Happily-Coding/SweepyWay/research case 2025-08-03/Pensando como encarar handrest.png

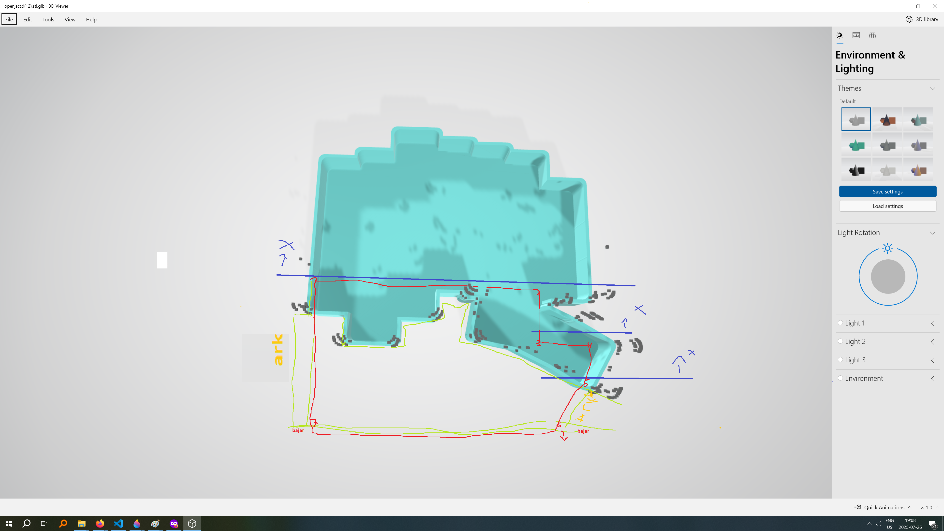
research case 2025-08-03/Pensando como encarar handrest.png
