Happily-Coding/SweepyWay/filtered-output/pcbs/outlines/l_hand_rest_polygon.dxf

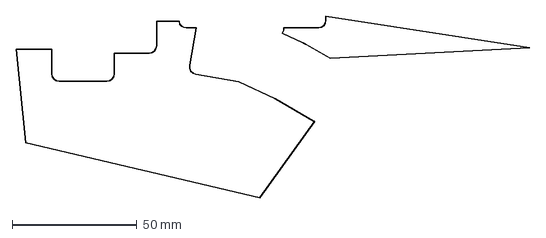
[picture p26: CAD file, 2026-02-16]
filtered-output/pcbs/outlines/l_hand_rest_polygon.dxf
206.0 x 72.7 mm
