Happily-Coding/SweepyWay/research case 2025-08-03/pymodeling_tests/lofted_polyhedron_clean.stl

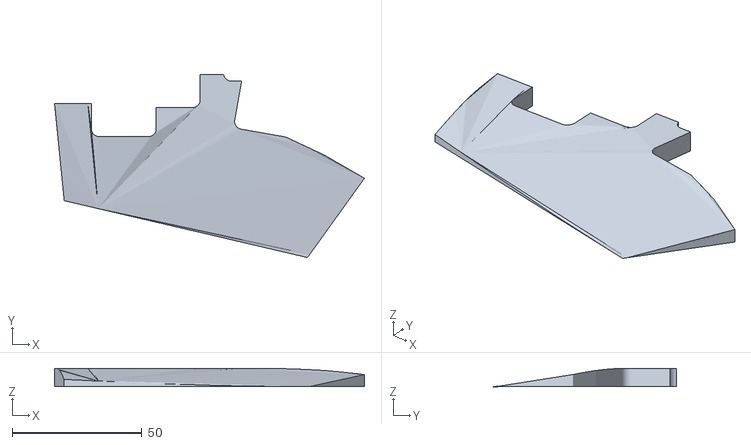
[picture p27: CAD file, 2025-08-17]
research case 2025-08-03/pymodeling_tests/lofted_polyhedron_clean.stl
119.6 x 70.7 x 7.00
