Happily-Coding/SweepyWay/filtered-output/pcbs/outlines/r_controller_area_border.dxf

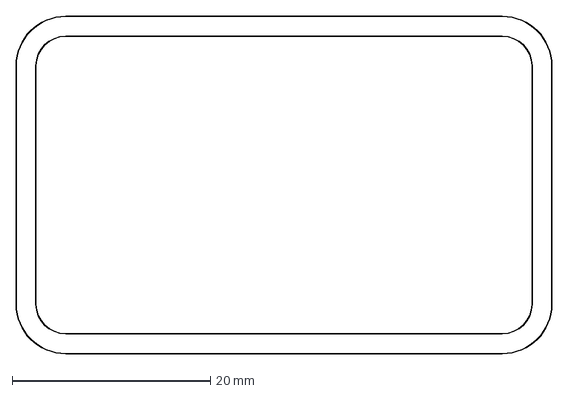
[picture p28: CAD file, 2026-02-16]
filtered-output/pcbs/outlines/r_controller_area_border.dxf
54.0 x 34.0 mm
