Happily-Coding/SweepyWay/research case 2025-08-03/pymodeling_tests/solid_lofted_mesh.stl

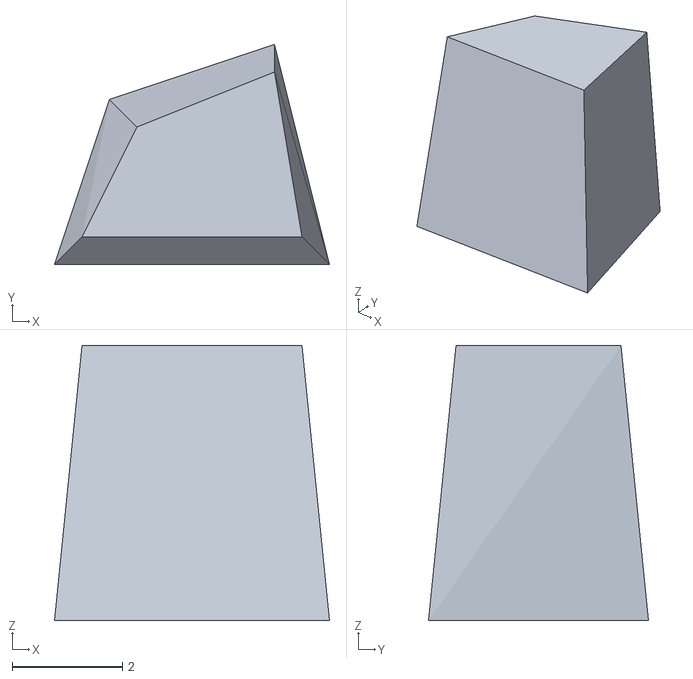
[picture p29: CAD file, 2025-08-17]
research case 2025-08-03/pymodeling_tests/solid_lofted_mesh.stl
5.00 x 4.00 x 5.00
