Happily-Coding/SweepyWay/filtered-output/pcbs/outlines/l_pcb_outline.dxf

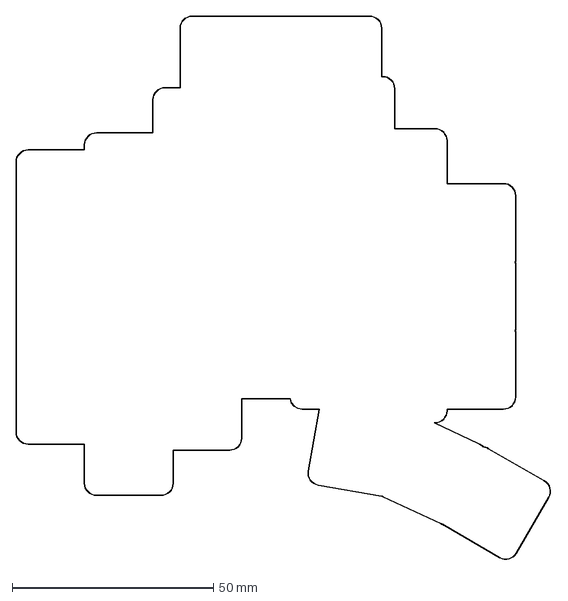
[picture p30: CAD file, 2026-02-16]
filtered-output/pcbs/outlines/l_pcb_outline.dxf
133.0 x 135.2 mm
