Happily-Coding/SweepyWay/research case 2025-08-03/pymodeling_tests/lofted_polyhedron.stl

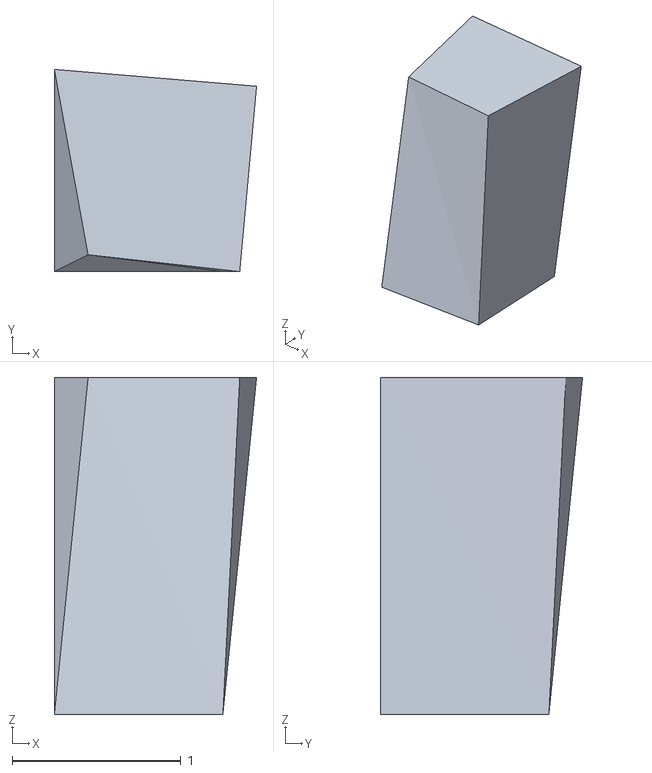
[picture p31: CAD file, 2025-08-17]
research case 2025-08-03/pymodeling_tests/lofted_polyhedron.stl
1.20 x 1.20 x 2.00
