Happily-Coding/SweepyWay/filtered-output/pcbs/outlines/l_tenting_base_bottom_outline.dxf

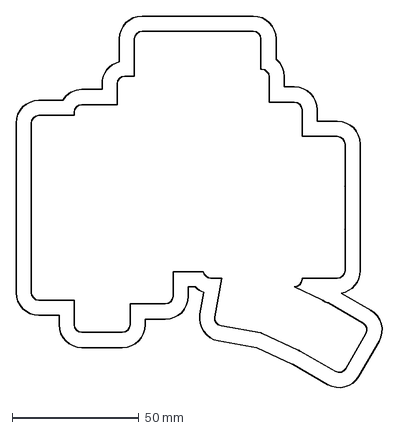
[picture p32: CAD file, 2026-02-16]
filtered-output/pcbs/outlines/l_tenting_base_bottom_outline.dxf
144.9 x 148.1 mm
