Happily-Coding/SweepyWay/research case 2025-08-03/pymodeling_tests/l_hand_rest_polygon.dxf

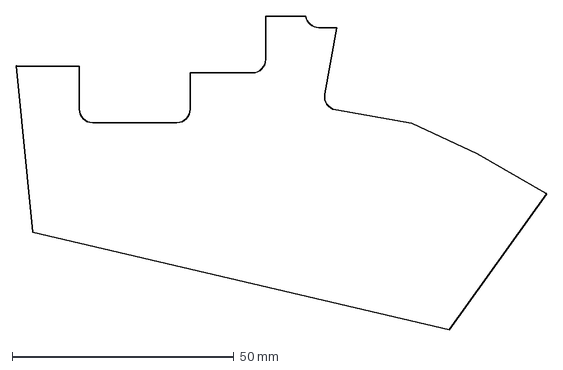
[picture p33: CAD file, 2025-08-17]
research case 2025-08-03/pymodeling_tests/l_hand_rest_polygon.dxf
119.6 x 70.7 mm
