Happily-Coding/SweepyWay/filtered-output/pcbs/outlines/l_key_based_board_outline_with_extra_padding.dxf

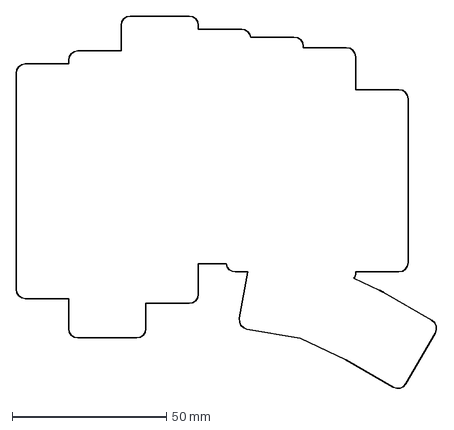
[picture p34: CAD file, 2026-02-16]
filtered-output/pcbs/outlines/l_key_based_board_outline_with_extra_padding.dxf
136.6 x 121.0 mm
