Happily-Coding/SweepyWay/research case 2025-08-03/pymodeling_tests/lofted_polyhedron_from_dxf.stl

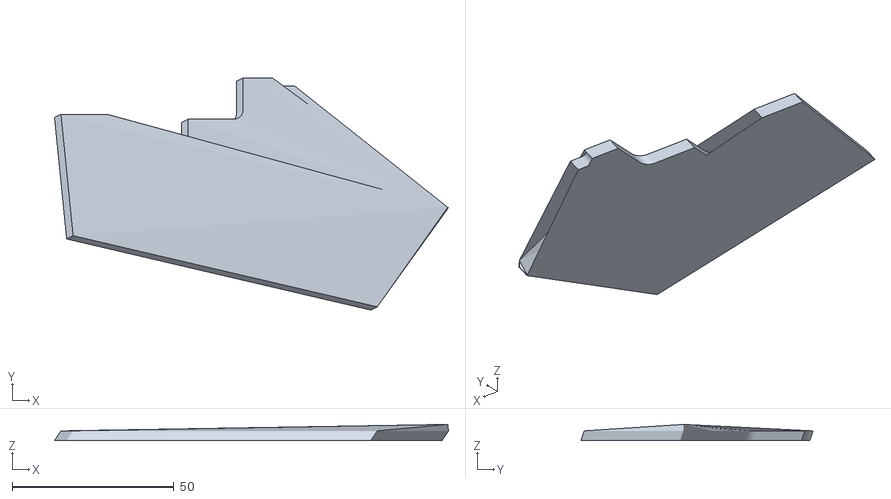
[picture p35: CAD file, 2025-08-17]
research case 2025-08-03/pymodeling_tests/lofted_polyhedron_from_dxf.stl
121.6 x 71.7 x 5.00
