Happily-Coding/SweepyWay/filtered-output/pcbs/outlines/r_case_border_do_not_ocupy.dxf

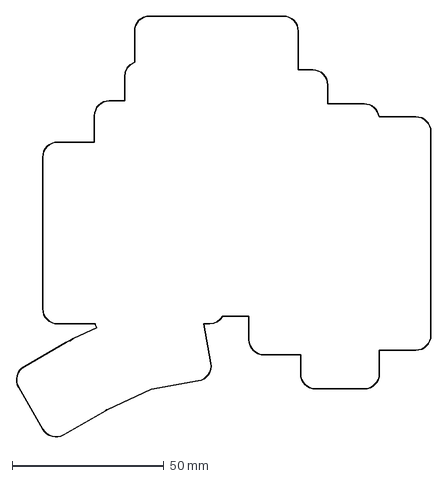
[picture p36: CAD file, 2026-02-16]
filtered-output/pcbs/outlines/r_case_border_do_not_ocupy.dxf
136.8 x 139.5 mm
