Happily-Coding/SweepyWay/filtered-output/pcbs/outlines/l_jsph_area_border.dxf

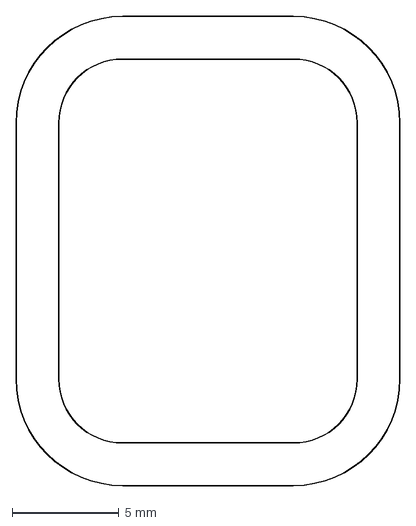
[picture p37: CAD file, 2026-02-16]
filtered-output/pcbs/outlines/l_jsph_area_border.dxf
18.0 x 22.0 mm
