Happily-Coding/SweepyWay/research case 2025-08-03/pymodeling_tests/l_hand_rest_solid_loft.stl

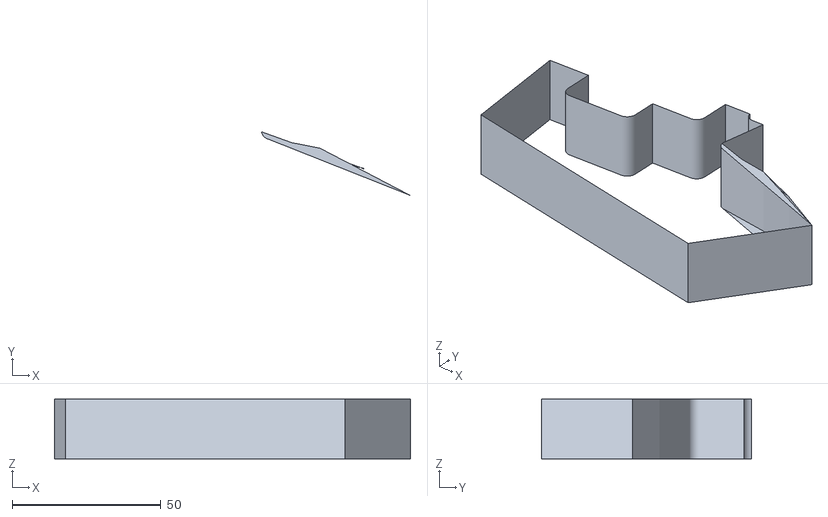
[picture p38: CAD file, 2025-08-17]
research case 2025-08-03/pymodeling_tests/l_hand_rest_solid_loft.stl
119.6 x 70.7 x 20.0
