Happily-Coding/SweepyWay/filtered-output/pcbs/outlines/l_key_based_board_outline.dxf

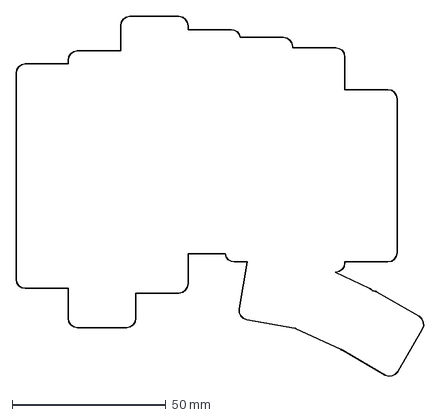
[picture p39: CAD file, 2026-02-16]
filtered-output/pcbs/outlines/l_key_based_board_outline.dxf
133.0 x 117.5 mm
