Happily-Coding/SweepyWay/research case 2025-08-03/pymodeling_tests/sloped_star_corrected.stl

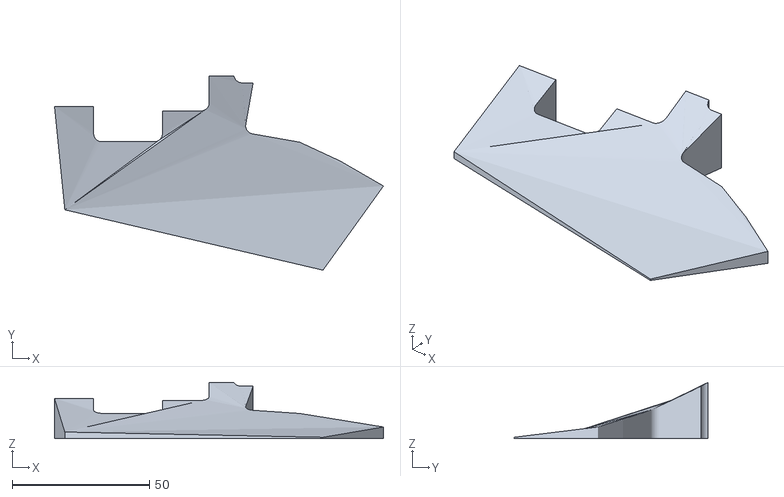
[picture p40: CAD file, 2025-08-17]
research case 2025-08-03/pymodeling_tests/sloped_star_corrected.stl
119.6 x 70.7 x 20.5
