Happily-Coding/SweepyWay/component_3d_models/m2-standoff-4mm.step

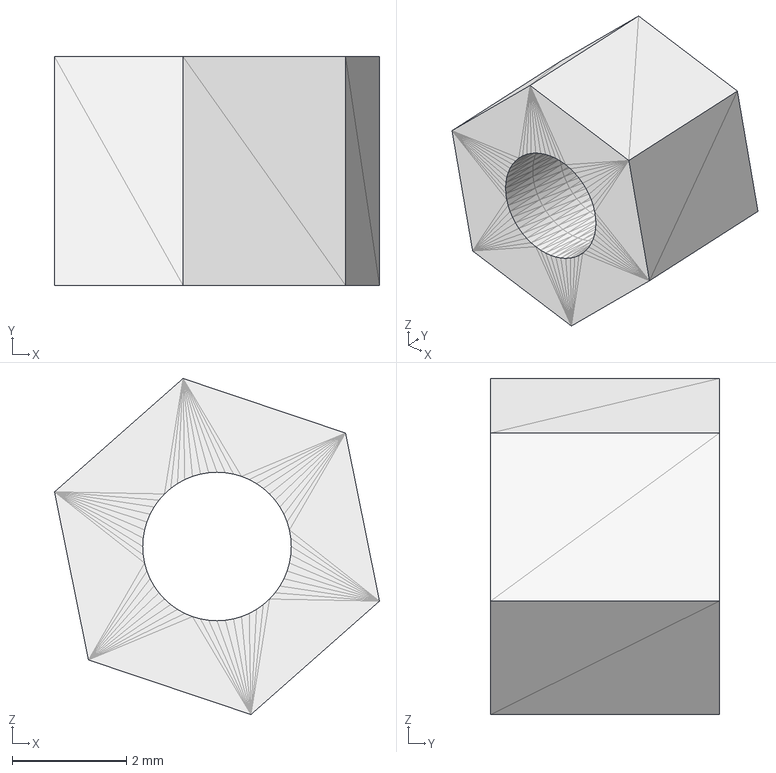
[picture p41: CAD file, 2026-02-16]
component_3d_models/m2-standoff-4mm.step
5.69 x 4.00 x 5.88 mm
