Happily-Coding/SweepyWay/filtered-output/pcbs/outlines/r_controller_area.dxf

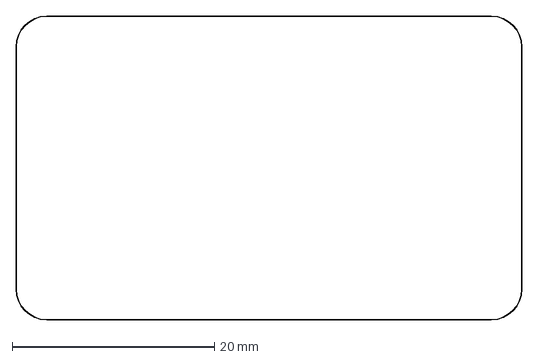
[picture p42: CAD file, 2026-02-16]
filtered-output/pcbs/outlines/r_controller_area.dxf
50.0 x 30.0 mm
