Happily-Coding/SweepyWay/research case 2025-08-03/pymodeling_tests/hand_rest_extruded.stl

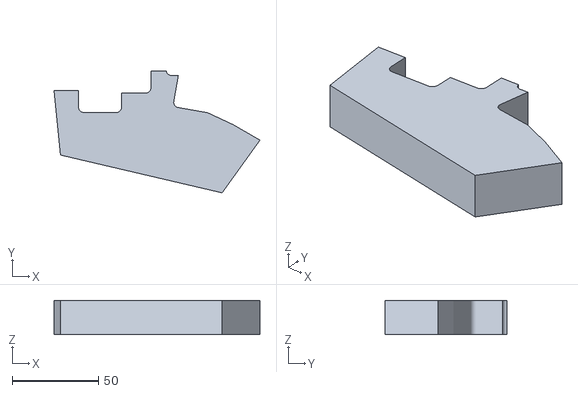
[picture p43: CAD file, 2025-08-17]
research case 2025-08-03/pymodeling_tests/hand_rest_extruded.stl
119.6 x 70.7 x 20.0
