Happily-Coding/SweepyWay/component_3d_models/m2-standoff-5mm.step

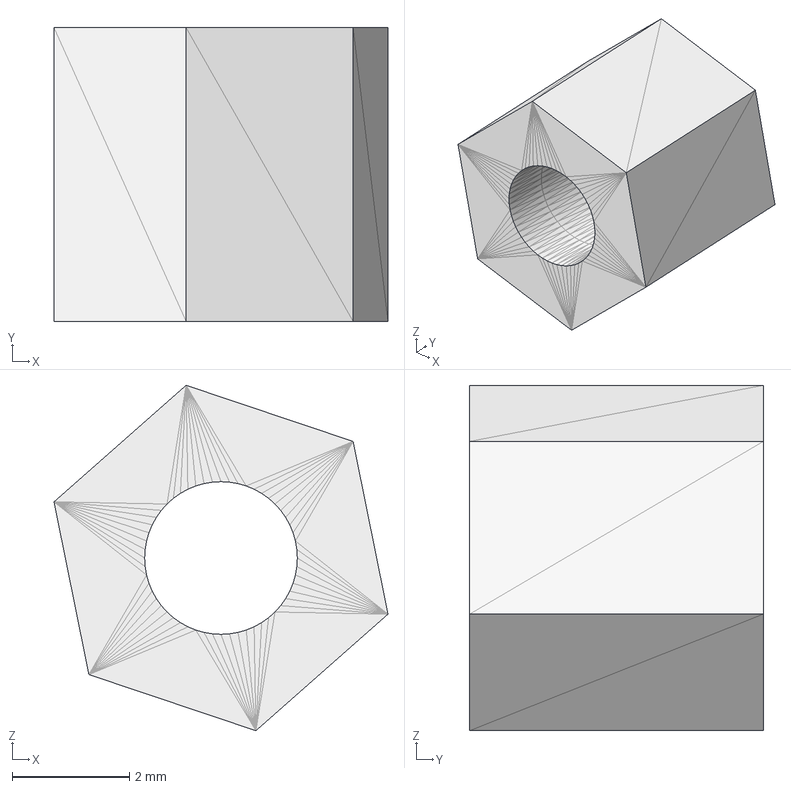
[picture p44: CAD file, 2026-02-16]
component_3d_models/m2-standoff-5mm.step
5.69 x 5.00 x 5.88 mm
