Happily-Coding/SweepyWay/filtered-output/pcbs/outlines/l_case_border_do_not_ocupy.dxf

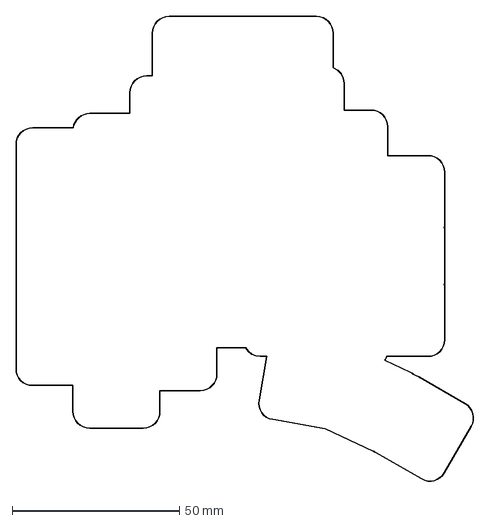
[picture p45: CAD file, 2026-02-16]
filtered-output/pcbs/outlines/l_case_border_do_not_ocupy.dxf
136.8 x 139.5 mm
