Happily-Coding/SweepyWay/research case 2025-08-03/pymodeling_tests/lofted_star_trimesh.stl

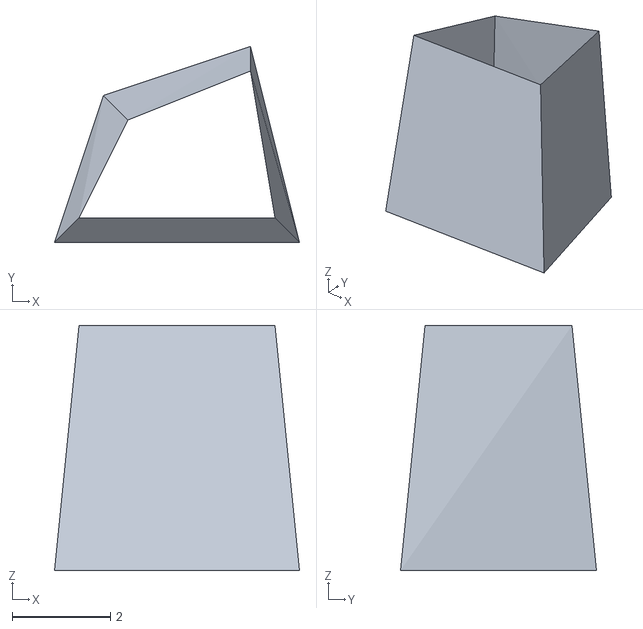
[picture p46: CAD file, 2025-08-17]
research case 2025-08-03/pymodeling_tests/lofted_star_trimesh.stl
5.00 x 4.00 x 5.00
