Happily-Coding/SweepyWay/component_3d_models/cross_recessed_phillips_countersunk_flat_head_M3x12.step

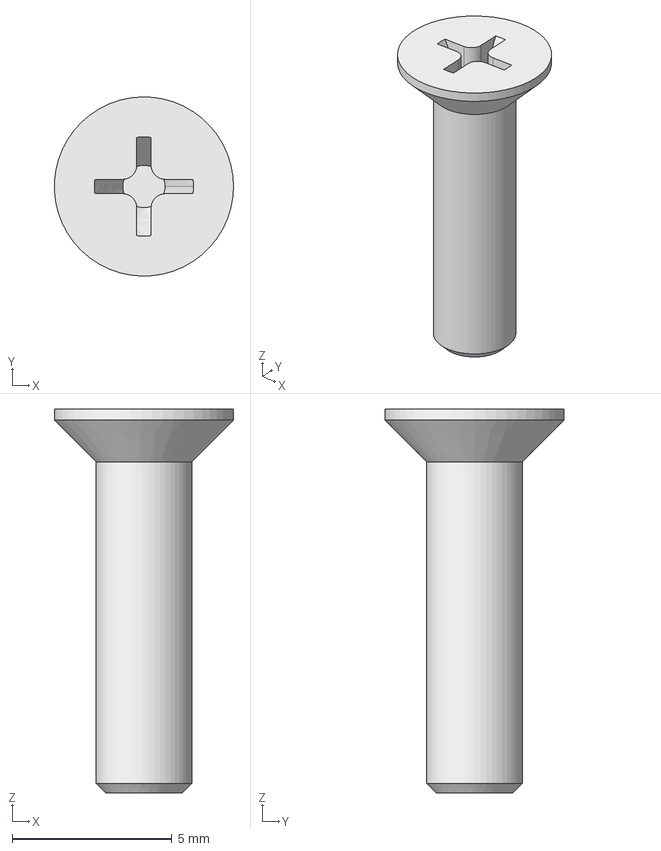
[picture p47: CAD file, 2026-02-15]
component_3d_models/cross_recessed_phillips_countersunk_flat_head_M3x12.step
5.59 x 5.60 x 12.0 mm
