Happily-Coding/SweepyWay/research case 2025-08-03/pymodeling_tests/lofted_polyhedron_refactored.stl

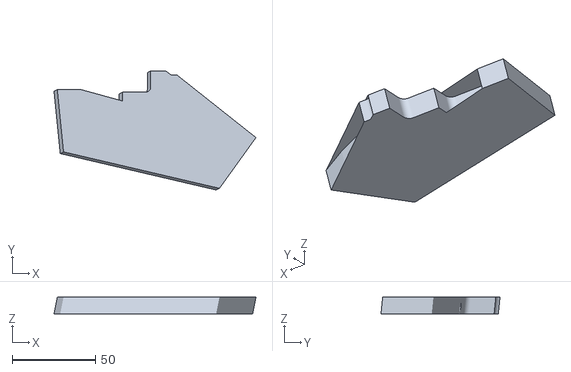
[picture p49: CAD file, 2025-08-17]
research case 2025-08-03/pymodeling_tests/lofted_polyhedron_refactored.stl
121.6 x 71.7 x 10.0
