Happily-Coding/SweepyWay/component_3d_models/cross_recessed_phillips_countersunk_flat_head_M3x10.step

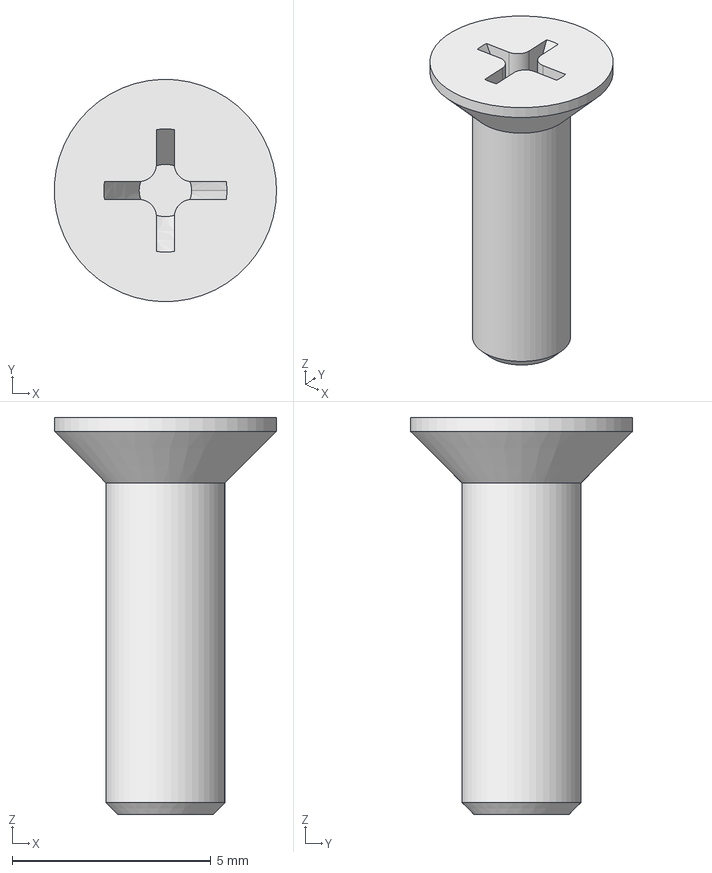
[picture p50: CAD file, 2026-02-15]
component_3d_models/cross_recessed_phillips_countersunk_flat_head_M3x10.step
5.59 x 5.60 x 10.0 mm
