Happily-Coding/SweepyWay/filtered-output/pcbs/outlines/l_cover_outline.dxf

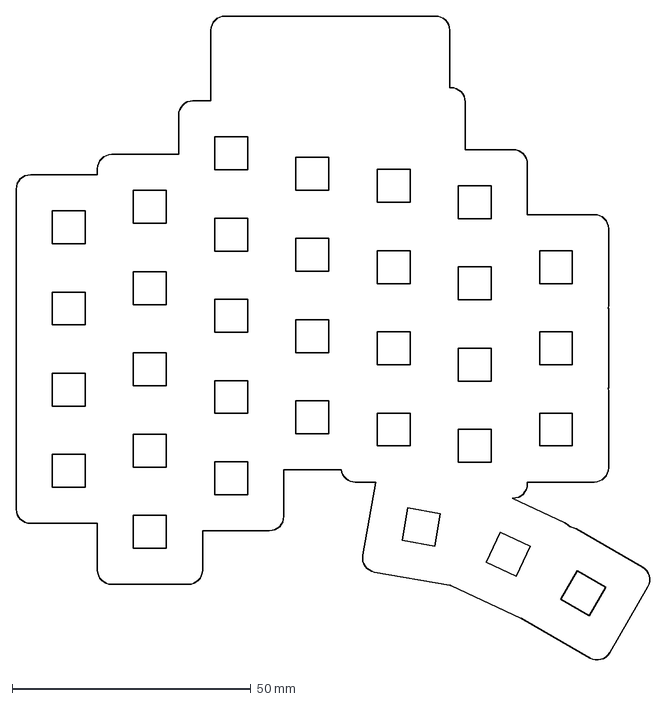
[picture p51: CAD file, 2026-02-16]
filtered-output/pcbs/outlines/l_cover_outline.dxf
133.0 x 135.2 mm
