Happily-Coding/SweepyWay/research case 2025-08-03/pymodeling_tests/l_hand_rest_lofted.stl

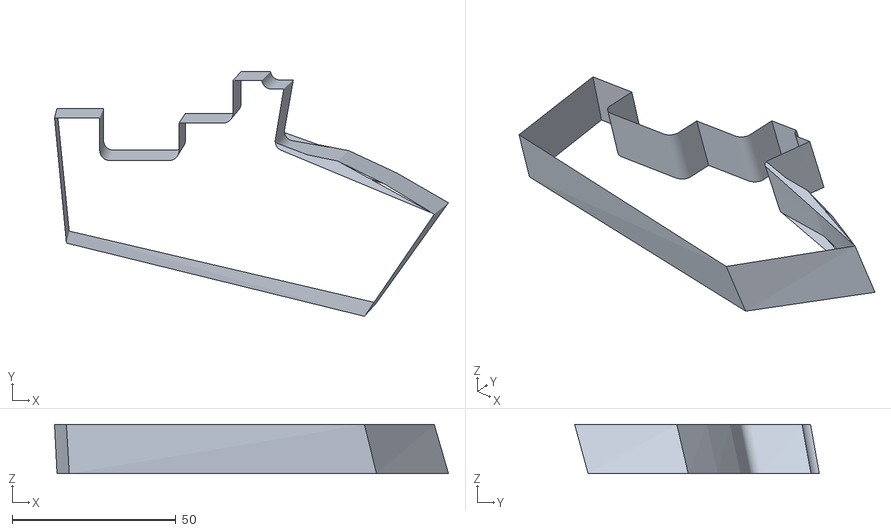
[picture p52: CAD file, 2025-08-17]
research case 2025-08-03/pymodeling_tests/l_hand_rest_lofted.stl
120.4 x 74.8 x 15.0
