Happily-Coding/SweepyWay/filtered-output/pcbs/outlines/l_controler_area_to_not_fill.dxf

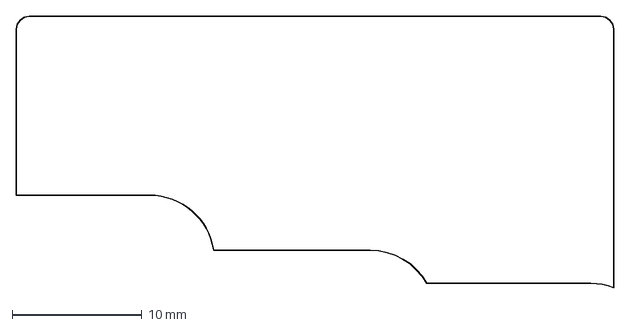
[picture p54: CAD file, 2026-02-16]
filtered-output/pcbs/outlines/l_controler_area_to_not_fill.dxf
46.0 x 20.9 mm
