Happily-Coding/SweepyWay/component_3d_models/cross_recessed_phillips_countersunk_flat_head_M2.5x10.step

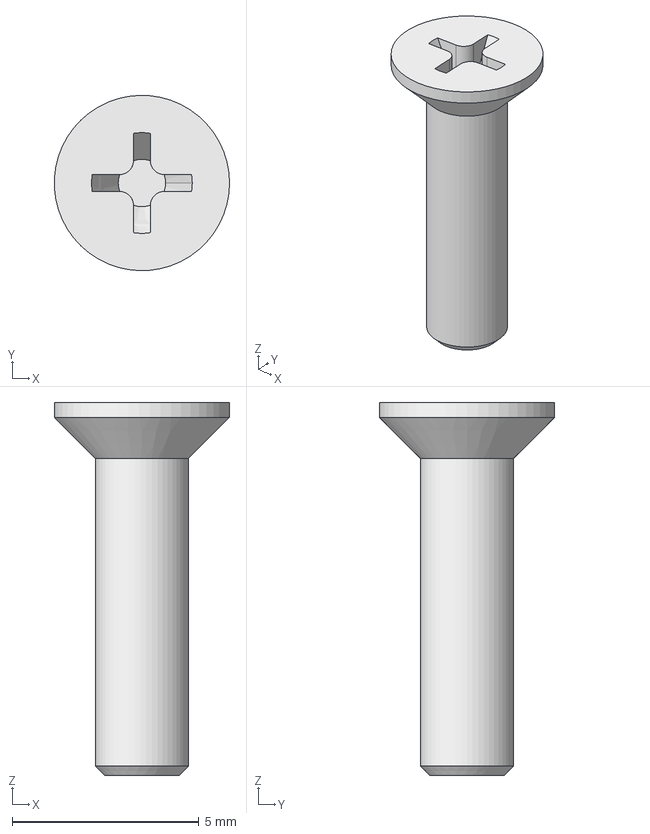
[picture p55: CAD file, 2026-02-15]
component_3d_models/cross_recessed_phillips_countersunk_flat_head_M2.5x10.step
4.70 x 4.70 x 10.0 mm
