Happily-Coding/SweepyWay/filtered-output/pcbs/outlines/r_case_bottom.dxf

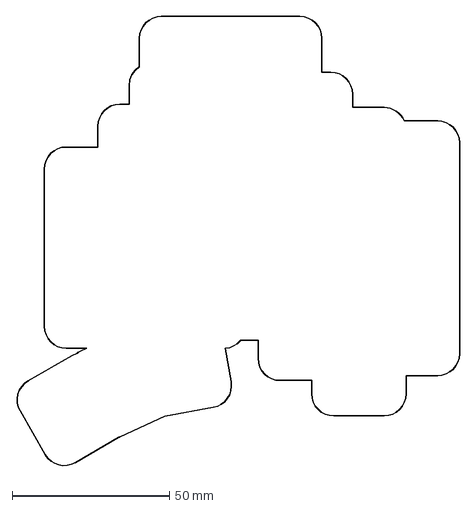
[picture p56: CAD file, 2026-02-16]
filtered-output/pcbs/outlines/r_case_bottom.dxf
140.9 x 143.8 mm
