Happily-Coding/SweepyWay/research case 2025-08-03/pymodeling_tests/star_lofted_basic.stl

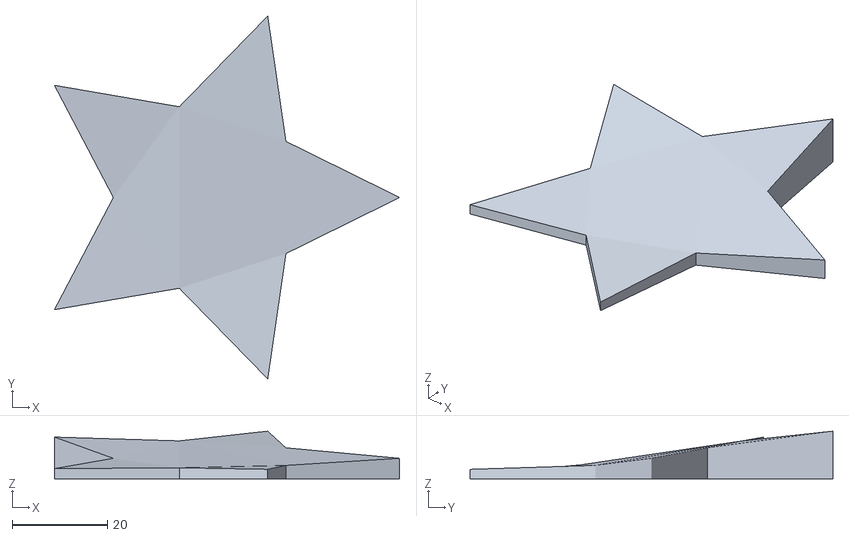
[picture p57: CAD file, 2025-08-17]
research case 2025-08-03/pymodeling_tests/star_lofted_basic.stl
72.4 x 76.1 x 10.0
