Happily-Coding/SweepyWay/filtered-output/pcbs/outlines/l_keys_outline.dxf

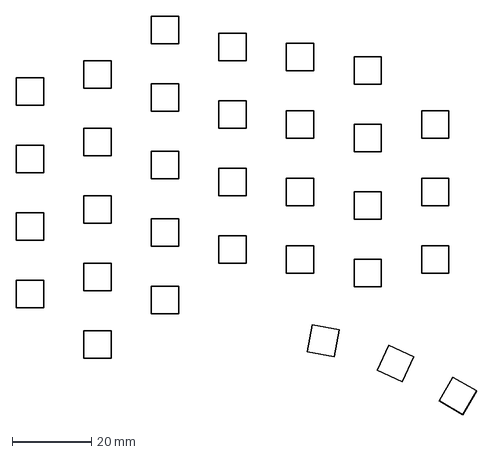
[picture p59: CAD file, 2026-02-16]
filtered-output/pcbs/outlines/l_keys_outline.dxf
115.9 x 100.3 mm
