Happily-Coding/SweepyWay/component_3d_models/cross_recessed_phillips_countersunk_flat_head_M2.5x06.step

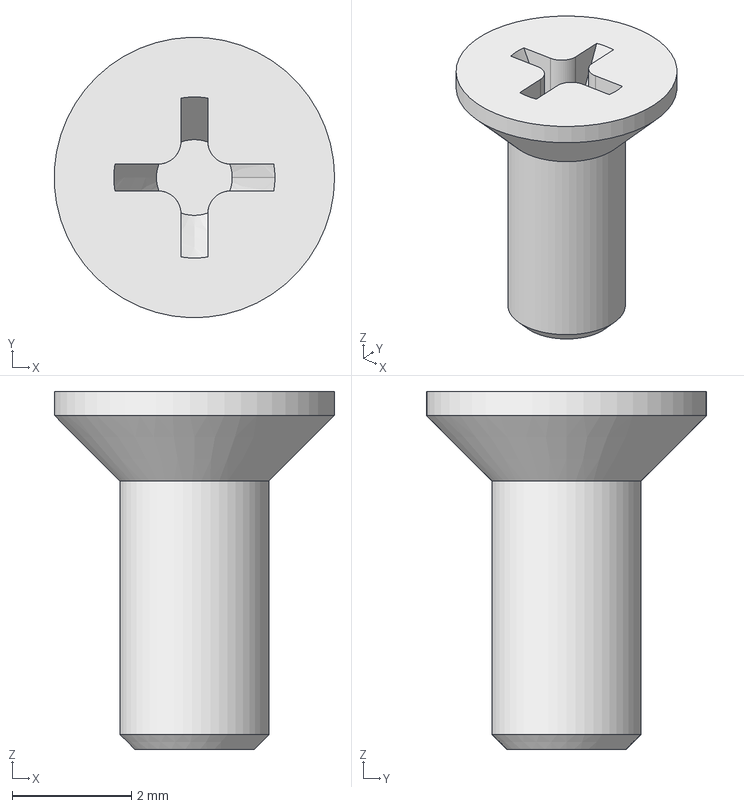
[picture p60: CAD file, 2026-02-15]
component_3d_models/cross_recessed_phillips_countersunk_flat_head_M2.5x06.step
4.70 x 4.70 x 6.00 mm
