Happily-Coding/SweepyWay/filtered-output/pcbs/outlines/l_jsph_area_cover.dxf

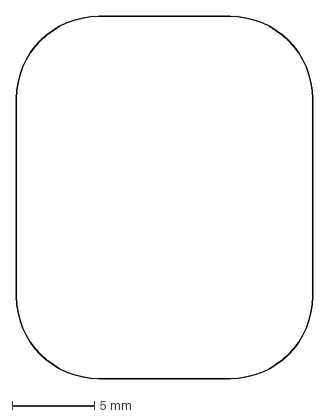
[picture p61: CAD file, 2026-02-16]
filtered-output/pcbs/outlines/l_jsph_area_cover.dxf
18.0 x 22.0 mm
