Happily-Coding/SweepyWay/research case 2025-08-03/pymodeling_tests/l_hand_rest_lofted_solid.stl

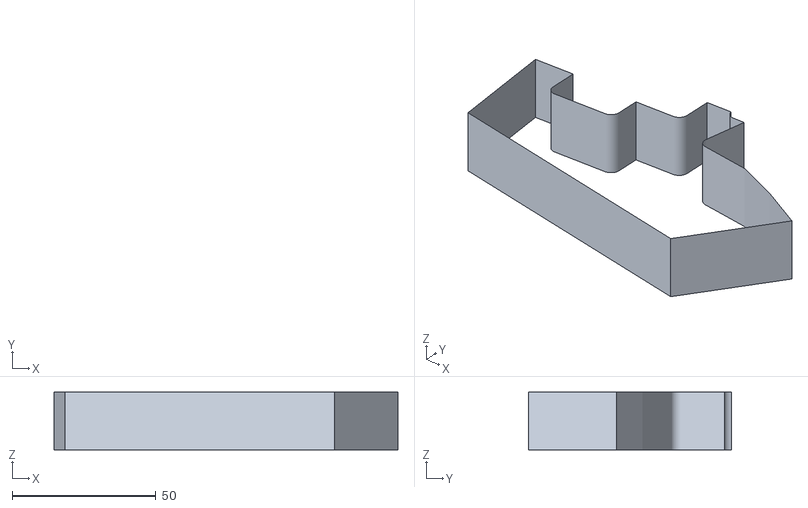
[picture p62: CAD file, 2025-08-17]
research case 2025-08-03/pymodeling_tests/l_hand_rest_lofted_solid.stl
119.6 x 70.7 x 20.0
