Happily-Coding/SweepyWay/component_3d_models/cross_recessed_phillips_countersunk_flat_head_M3x04.step

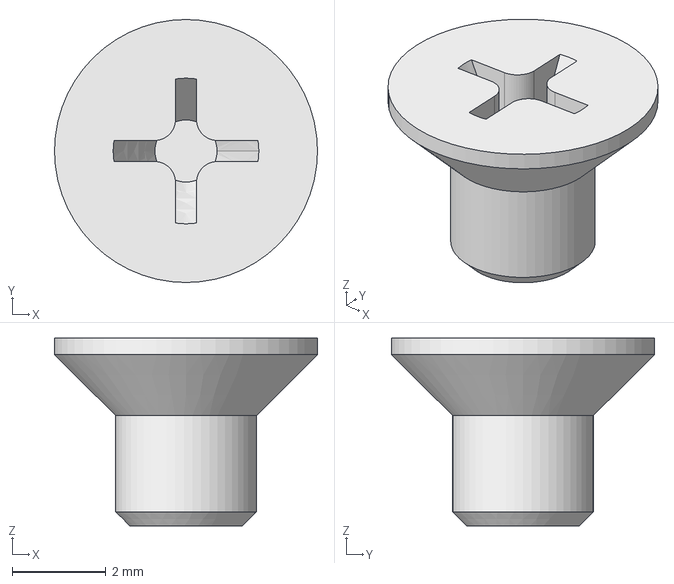
[picture p63: CAD file, 2026-02-15]
component_3d_models/cross_recessed_phillips_countersunk_flat_head_M3x04.step
5.60 x 5.60 x 4.00 mm
