Happily-Coding/SweepyWay/filtered-output/pcbs/outlines/l_controller_area_to_cover_outline.dxf

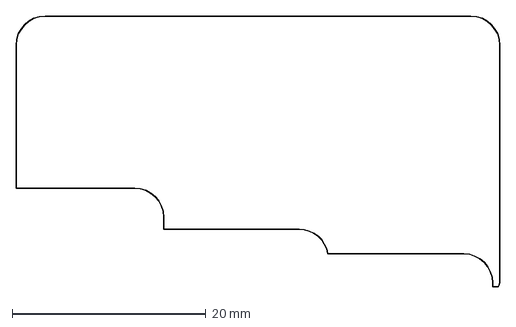
[picture p64: CAD file, 2026-02-16]
filtered-output/pcbs/outlines/l_controller_area_to_cover_outline.dxf
50.0 x 28.0 mm
