Happily-Coding/SweepyWay/research case 2025-08-03/pymodeling_tests/sloped_cube.stl

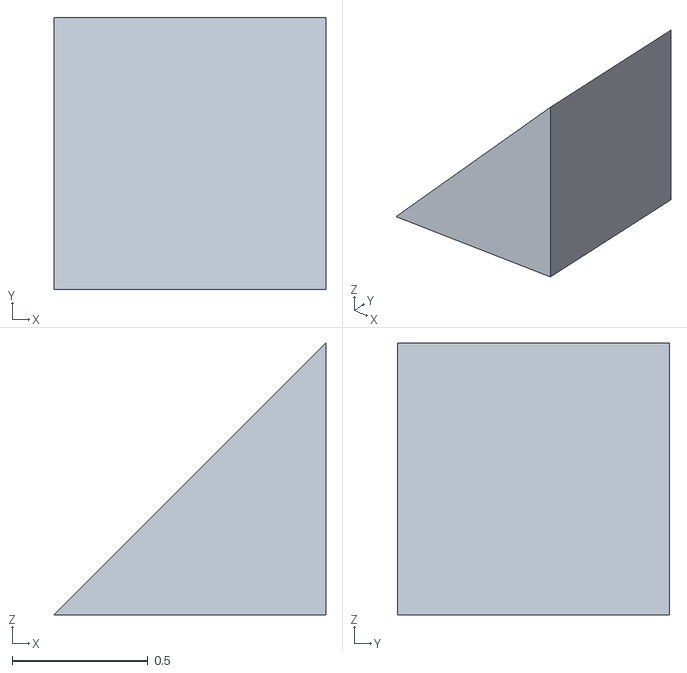
[picture p65: CAD file, 2025-08-17]
research case 2025-08-03/pymodeling_tests/sloped_cube.stl
1.00 x 1.00 x 1.00
