Happily-Coding/SweepyWay/filtered-output/pcbs/outlines/l_usbc_border_outline.dxf

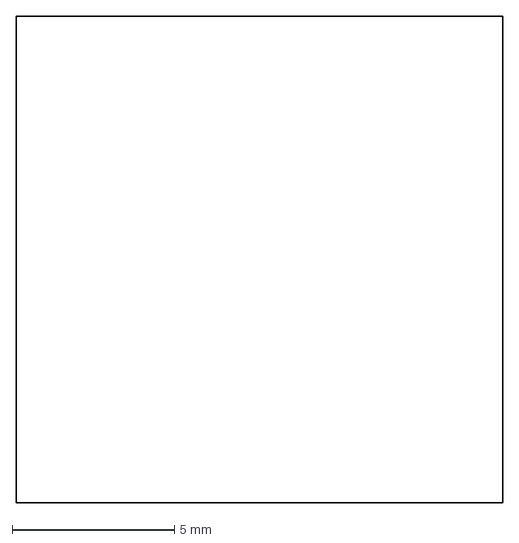
[picture p67: CAD file, 2026-02-16]
filtered-output/pcbs/outlines/l_usbc_border_outline.dxf
15.0 x 15.0 mm
