Happily-Coding/SweepyWay/filtered-output/pcbs/outlines/r_case_border.dxf

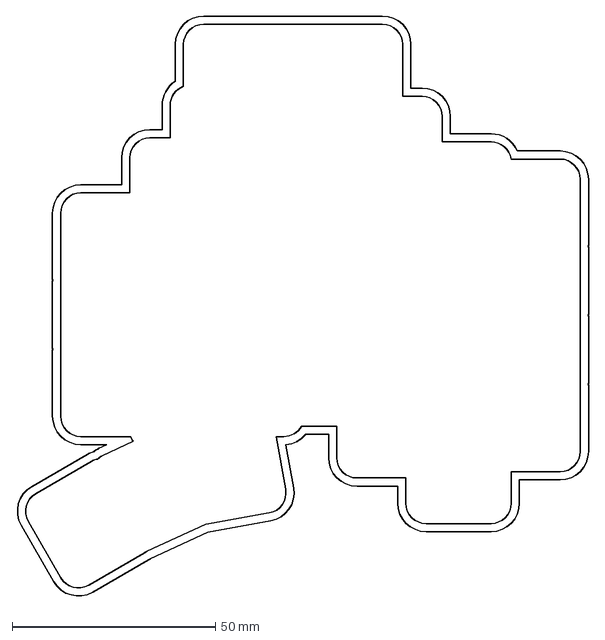
[picture p69: CAD file, 2026-02-16]
filtered-output/pcbs/outlines/r_case_border.dxf
140.9 x 143.8 mm
