Happily-Coding/SweepyWay/research case 2025-08-03/pymodeling_tests/lofted_polyhedron_optb.stl

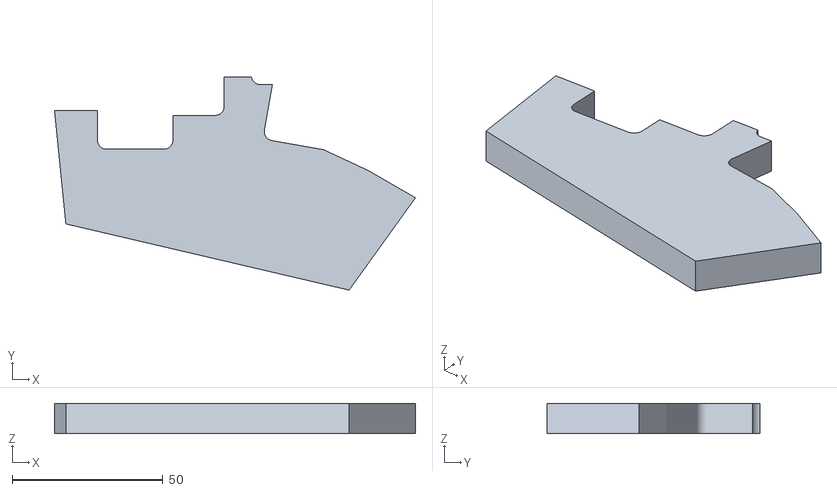
[picture p70: CAD file, 2025-08-17]
research case 2025-08-03/pymodeling_tests/lofted_polyhedron_optb.stl
119.6 x 70.7 x 10.0
