Happily-Coding/SweepyWay/component_3d_models/cross_recessed_phillips_countersunk_flat_head_M2.5x05.step

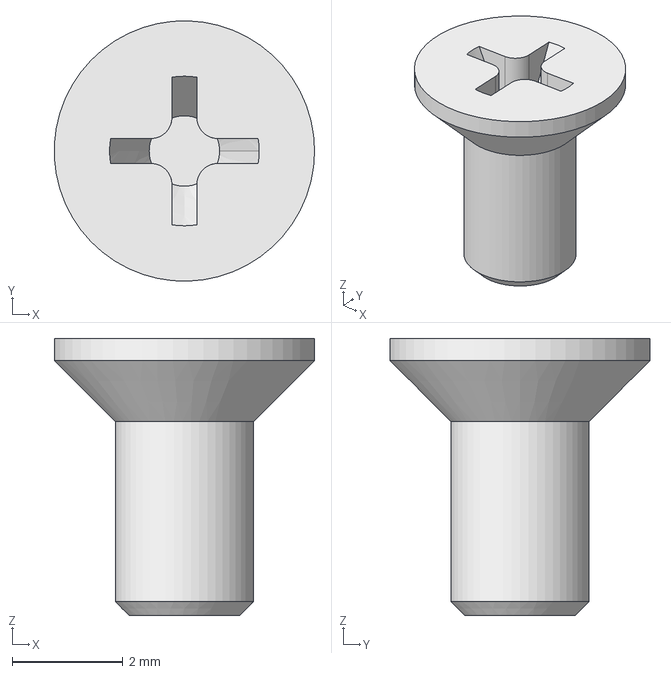
[picture p71: CAD file, 2026-02-15]
component_3d_models/cross_recessed_phillips_countersunk_flat_head_M2.5x05.step
4.70 x 4.70 x 5.00 mm
