Happily-Coding/SweepyWay/filtered-output/pcbs/outlines/l_jsph_area.dxf

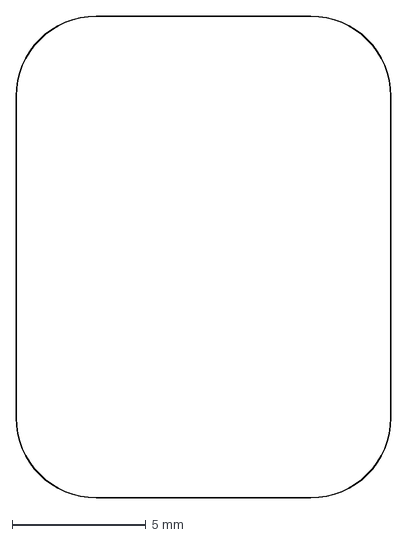
[picture p72: CAD file, 2026-02-16]
filtered-output/pcbs/outlines/l_jsph_area.dxf
14.0 x 18.0 mm
