Happily-Coding/SweepyWay/filtered-output/pcbs/outlines/r_coverpart_switch_plate_outline.dxf

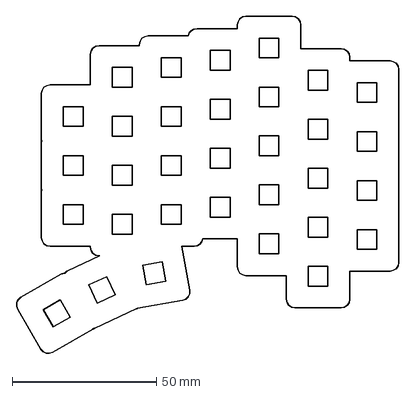
[picture p74: CAD file, 2026-02-16]
filtered-output/pcbs/outlines/r_coverpart_switch_plate_outline.dxf
132.7 x 117.5 mm
