Happily-Coding/SweepyWay/filtered-output/pcbs/outlines/l_thumb_suplementary_outline.dxf

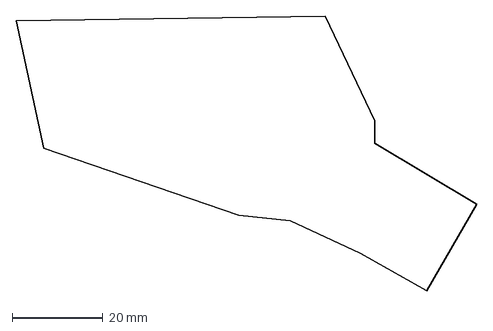
[picture p77: CAD file, 2026-02-16]
filtered-output/pcbs/outlines/l_thumb_suplementary_outline.dxf
101.4 x 60.4 mm
