Happily-Coding/SweepyWay/filtered-output/pcbs/outlines/r_cover_outline.dxf

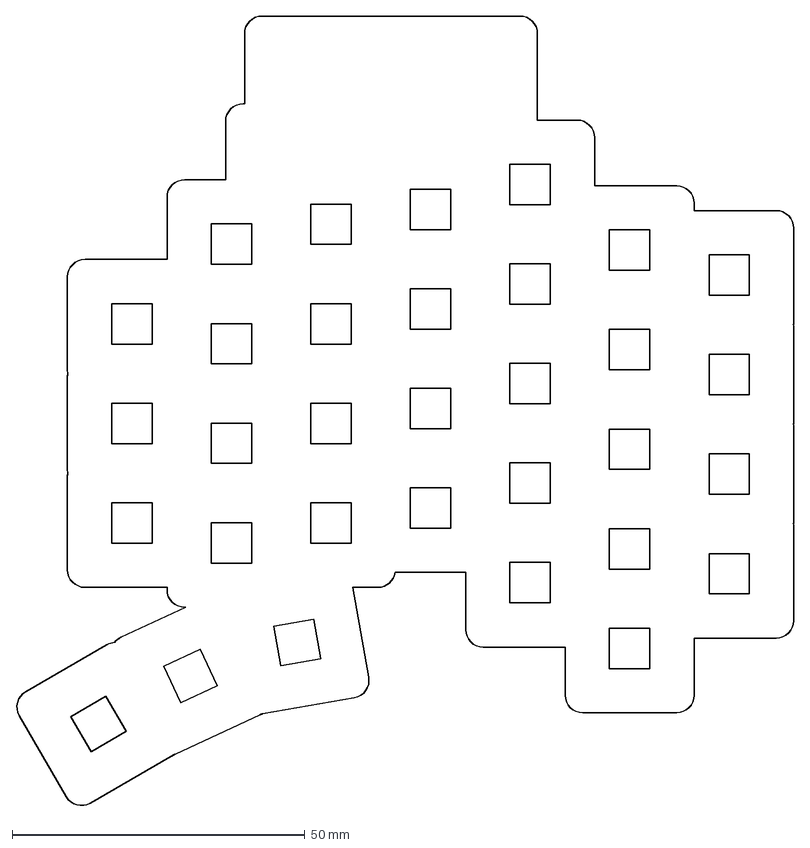
[picture p80: CAD file, 2026-02-16]
filtered-output/pcbs/outlines/r_cover_outline.dxf
132.7 x 135.2 mm
