Happily-Coding/SweepyWay/filtered-output/pcbs/outlines/l_controller_area_cover.dxf

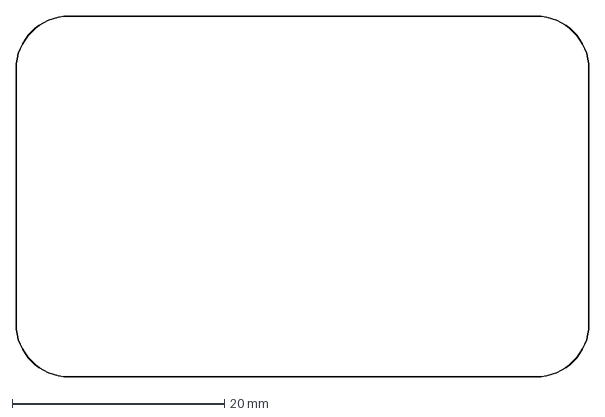
[picture p81: CAD file, 2026-02-16]
filtered-output/pcbs/outlines/l_controller_area_cover.dxf
54.0 x 34.0 mm
