Happily-Coding/SweepyWay/component_3d_models/m2-standoff-7mm.stl

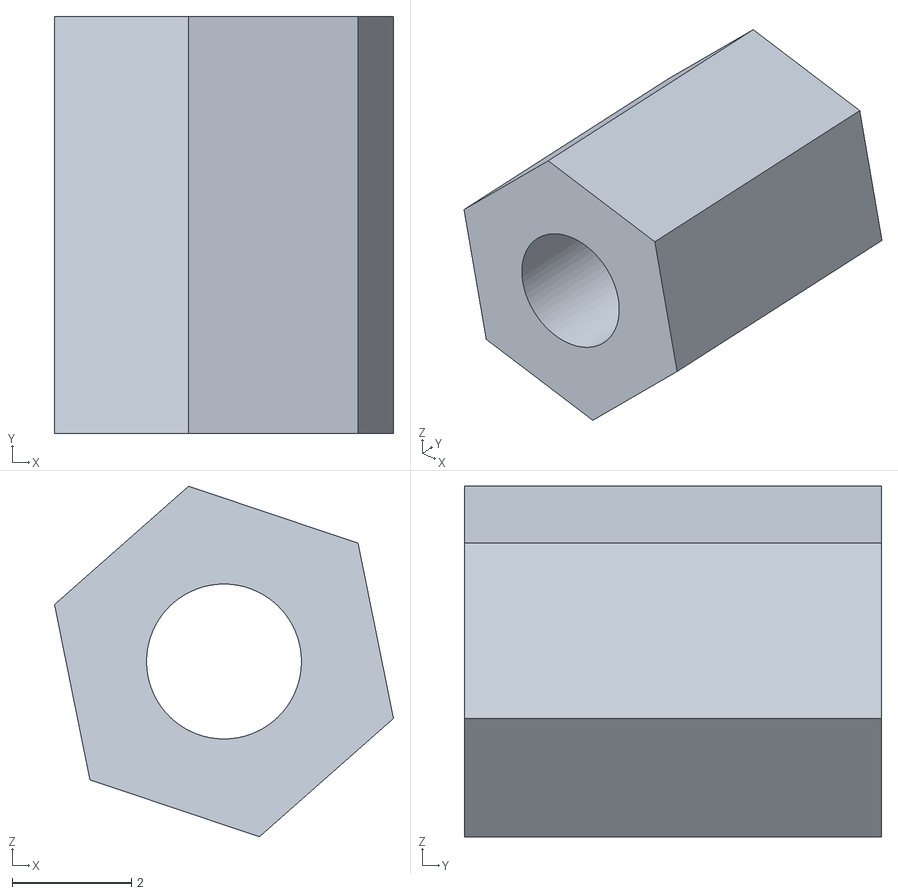
[picture p82: CAD file, 2026-02-15]
component_3d_models/m2-standoff-7mm.stl
5.69 x 7.00 x 5.88
