Happily-Coding/SweepyWay/component_3d_models/m2-standoff-9mm.stl

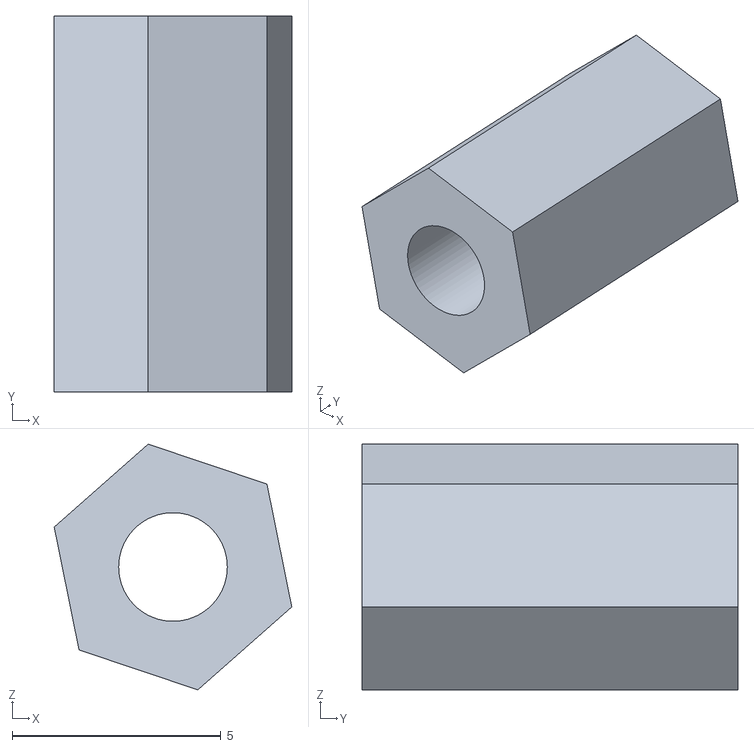
[picture p83: CAD file, 2026-02-15]
component_3d_models/m2-standoff-9mm.stl
5.69 x 9.00 x 5.88
