Happily-Coding/SweepyWay/component_3d_models/m2-standoff-3mm.stl

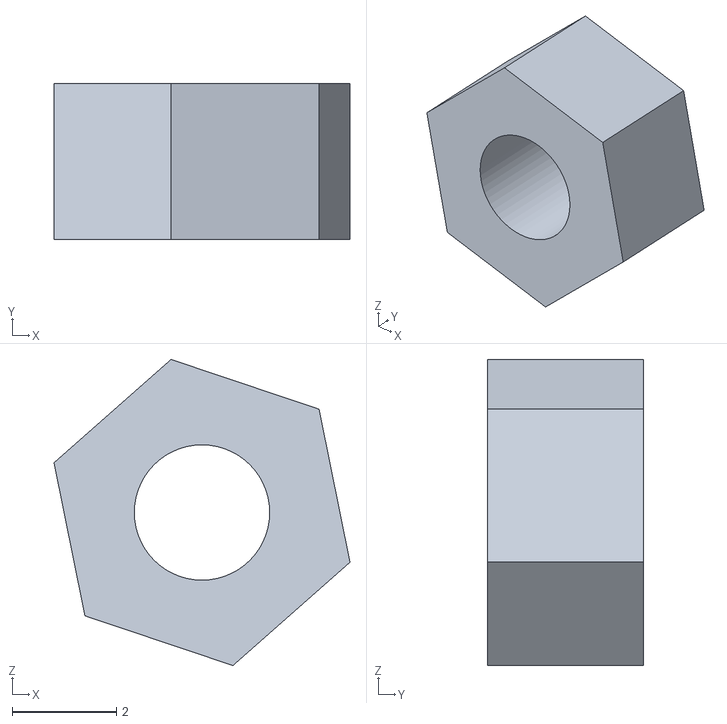
[picture p84: CAD file, 2026-02-15]
component_3d_models/m2-standoff-3mm.stl
5.69 x 3.00 x 5.88
