Happily-Coding/SweepyWay/component_3d_models/m2-standoff-8mm.stl

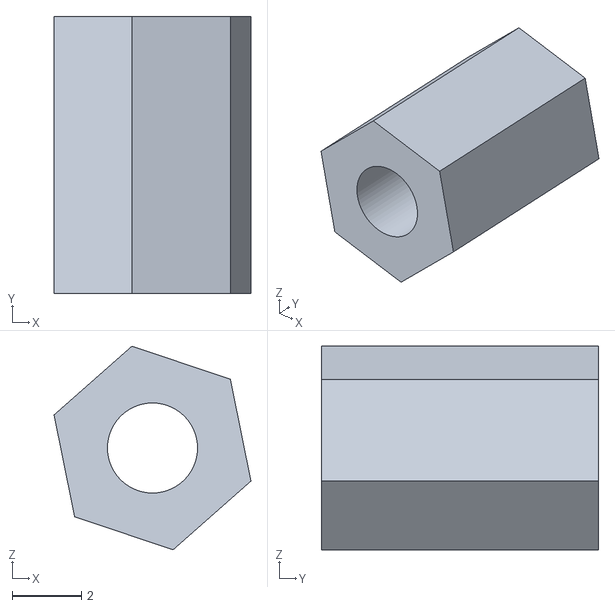
[picture p85: CAD file, 2026-02-15]
component_3d_models/m2-standoff-8mm.stl
5.69 x 8.00 x 5.88
