Happily-Coding/SweepyWay/component_3d_models/m2-standoff-1mm.stl

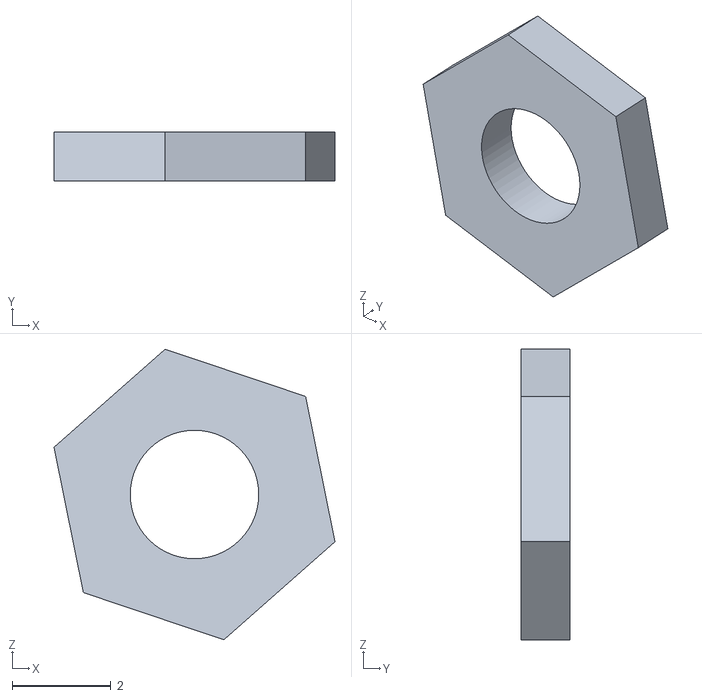
[picture p86: CAD file, 2026-02-15]
component_3d_models/m2-standoff-1mm.stl
5.69 x 1.00 x 5.88
