Happily-Coding/SweepyWay/component_3d_models/m2-standoff-2mm.stl

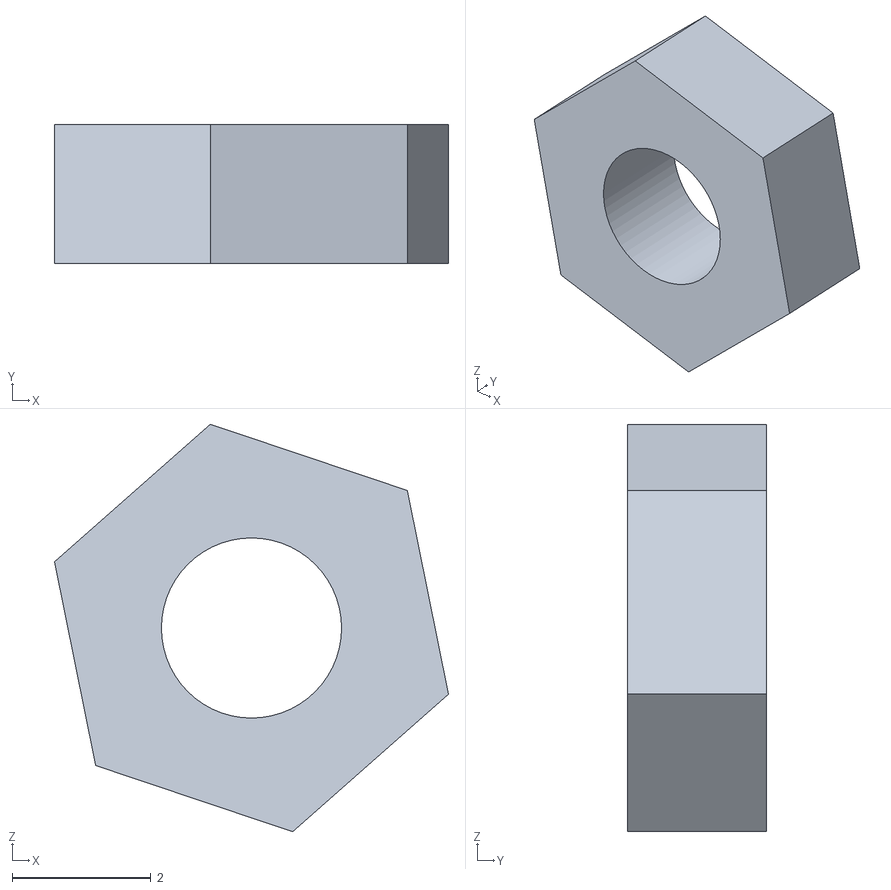
[picture p87: CAD file, 2026-02-15]
component_3d_models/m2-standoff-2mm.stl
5.69 x 2.00 x 5.88
