Happily-Coding/SweepyWay/component_3d_models/m2-standoff-6mm.stl

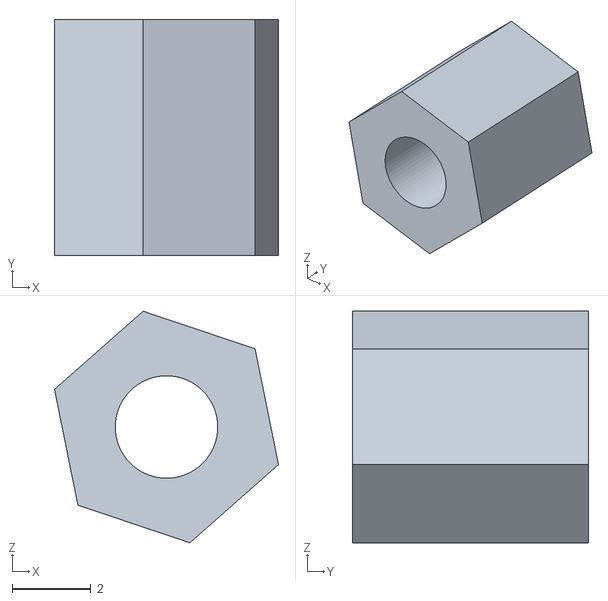
[picture p88: CAD file, 2026-02-15]
component_3d_models/m2-standoff-6mm.stl
5.69 x 6.00 x 5.88
