Happily-Coding/SweepyWay/component_3d_models/m2-standoff-10mm.stl

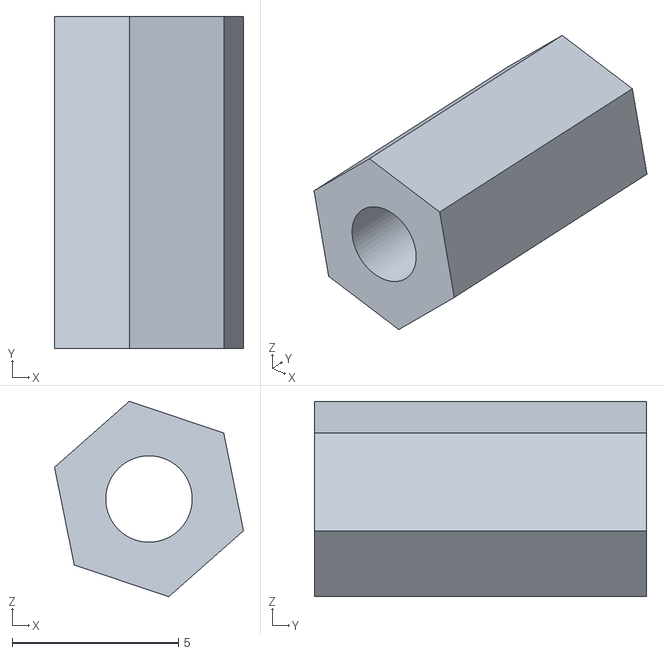
[picture p89: CAD file, 2026-02-15]
component_3d_models/m2-standoff-10mm.stl
5.69 x 10.0 x 5.88
