Happily-Coding/SweepyWay/component_3d_models/PinHeader_2.54mm_2x-12.step

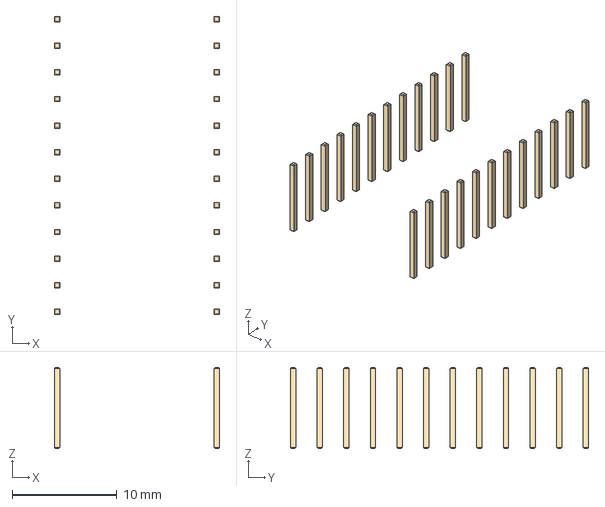
[picture p90: CAD file, 2026-02-13]
component_3d_models/PinHeader_2.54mm_2x-12.step
15.8 x 28.5 x 7.75 mm
