Happily-Coding/SweepyWay/component_3d_models/PinHeader_1x04_P2.54mm_Vertical.step

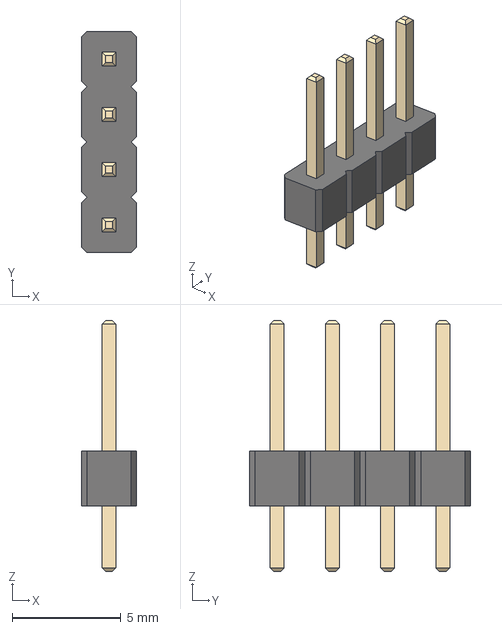
[picture p92: CAD file, 2026-02-13]
component_3d_models/PinHeader_1x04_P2.54mm_Vertical.step
2.54 x 10.2 x 11.5 mm
