Happily-Coding/SweepyWay/component_3d_models/PinHeader_1x10_P2.54mm_Vertical.step

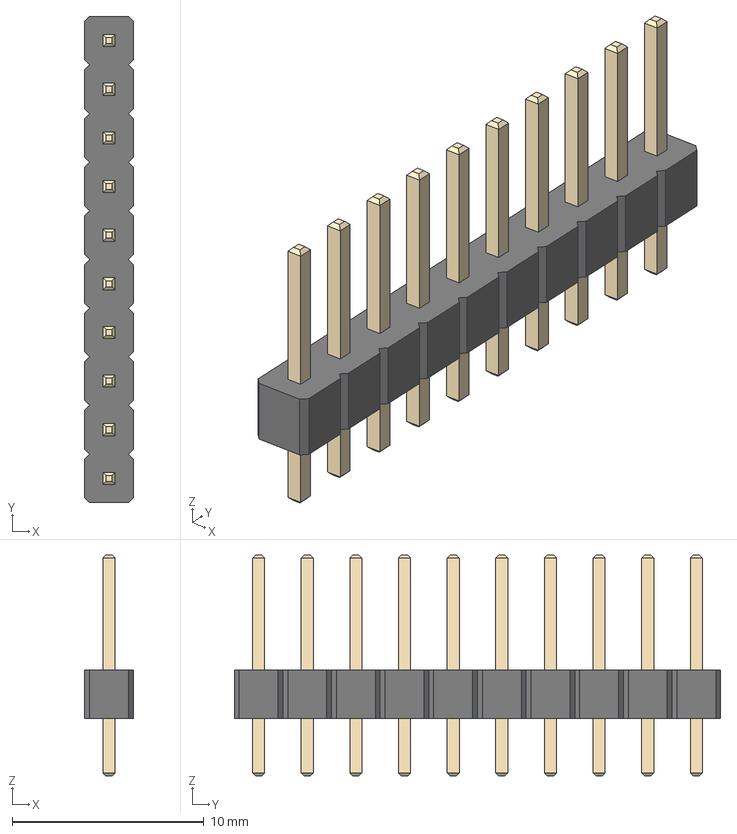
[picture p94: CAD file, 2026-02-13]
component_3d_models/PinHeader_1x10_P2.54mm_Vertical.step
2.54 x 25.4 x 11.5 mm
