Happily-Coding/SweepyWay/component_3d_models/JSTPH2-S2B-PH-K-S-LF-SN.STEP

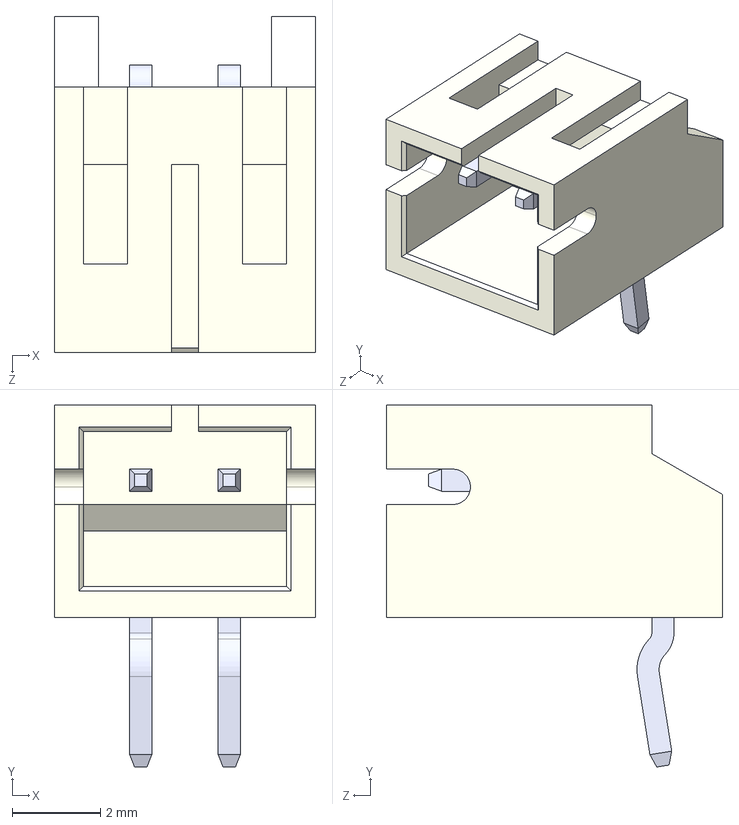
[picture p97: CAD file, 2026-02-07]
component_3d_models/JSTPH2-S2B-PH-K-S-LF-SN.STEP
5.90 x 8.18 x 7.60 mm
