Happily-Coding/SweepyWay/component_3d_models/SSSS811101--3DModel-STEP-269445.STEP

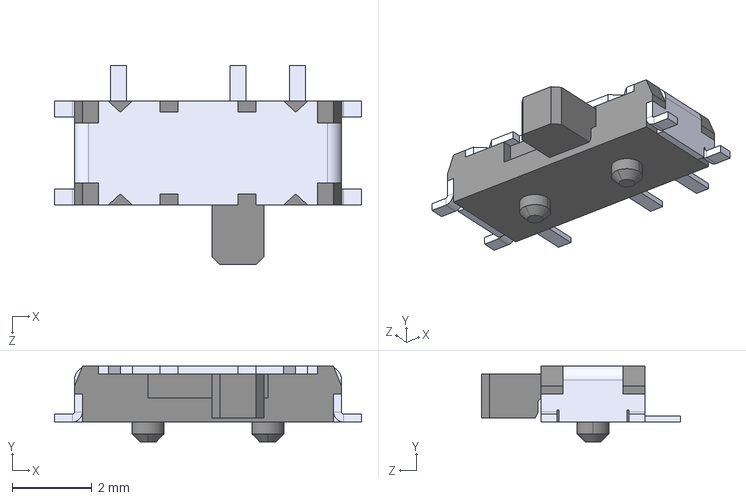
[picture p98: CAD file, 2026-02-01]
component_3d_models/SSSS811101--3DModel-STEP-269445.STEP
7.70 x 1.90 x 5.00 mm
