Happily-Coding/SweepyWay/component_3d_models/D_SOD-123.step

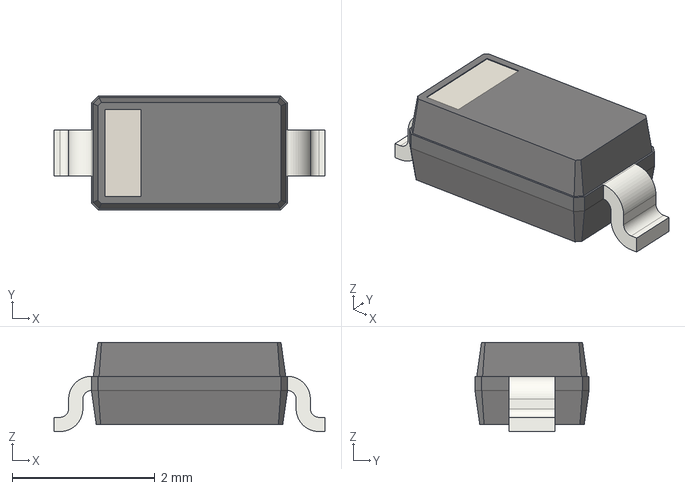
[picture p99: CAD file, 2026-02-01]
component_3d_models/D_SOD-123.step
3.80 x 1.60 x 1.25 mm
