Happily-Coding/SweepyWay/component_3d_models/SW_SPST_EVQPE1.step

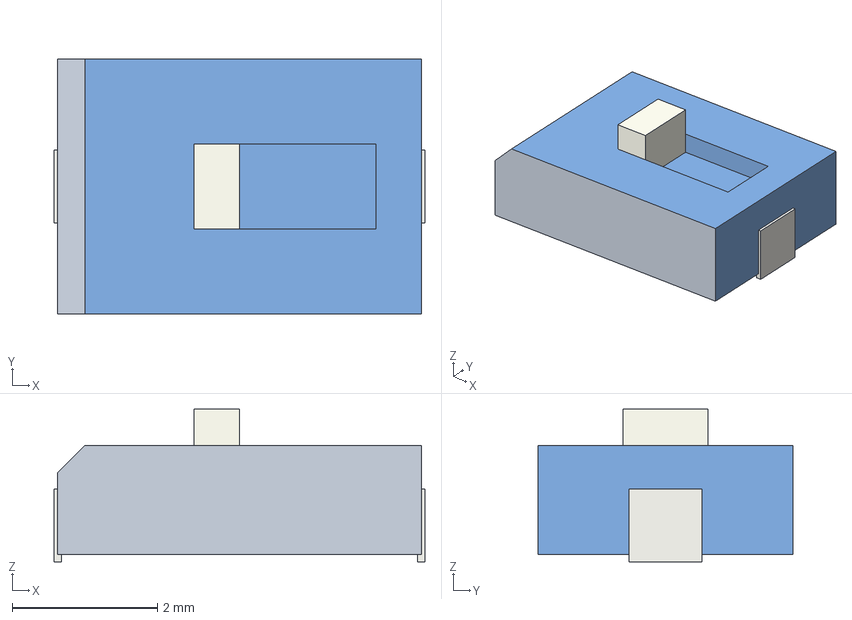
[picture p100: CAD file, 2026-02-01]
component_3d_models/SW_SPST_EVQPE1.step
5.10 x 3.50 x 2.10 mm
SW_SPST_EVQPE002
SW_SPST_EVQPE1
