Happily-Coding/SweepyWay/component_3d_models/EVQ-PUC02K.step

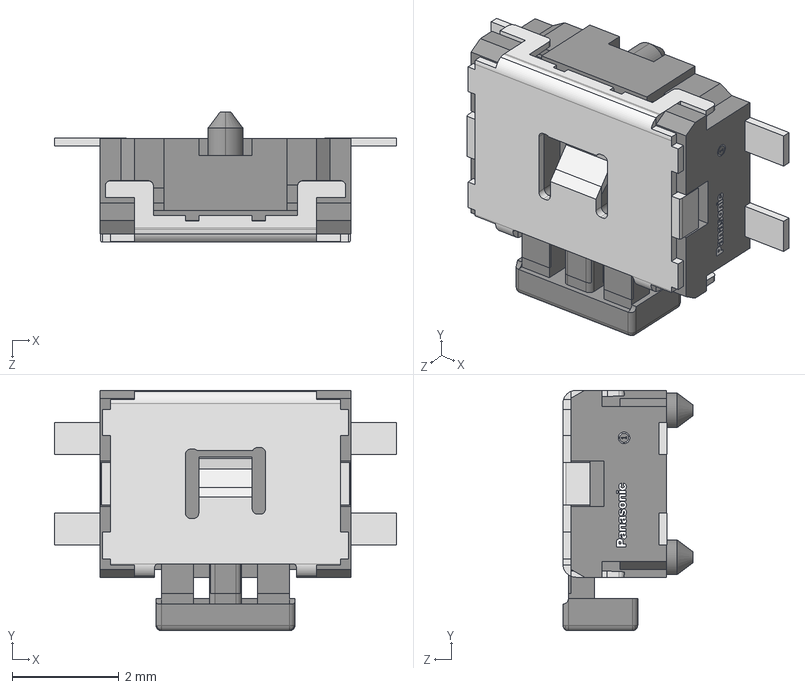
[picture p101: CAD file, 2026-02-01]
component_3d_models/EVQ-PUC02K.step
6.40 x 4.50 x 2.44 mm
EVQPU-KB-02K
Panasonic Logo
