Happily-Coding/SweepyWay/component_3d_models/Nice_Nano_V2.step

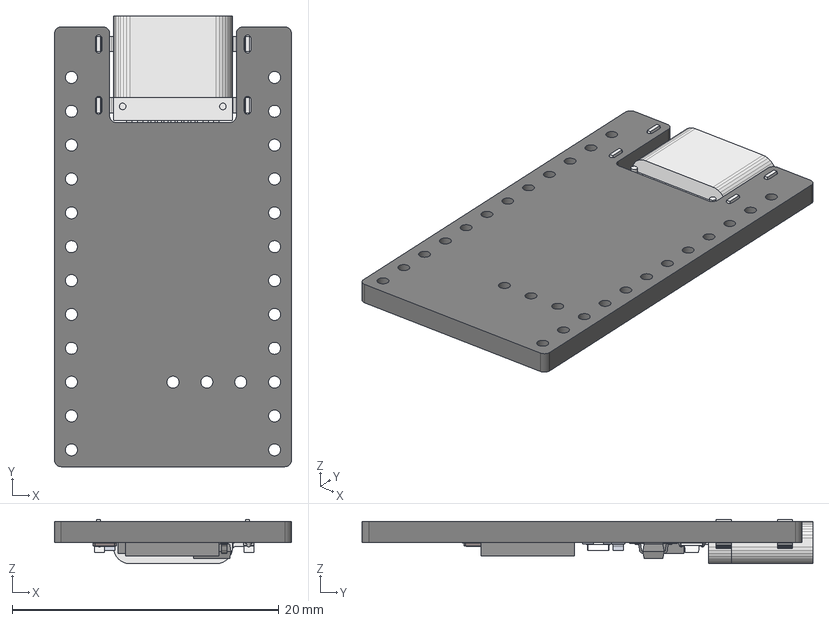
[picture p102: CAD file, 2026-01-31]
component_3d_models/Nice_Nano_V2.step
17.8 x 33.8 x 3.34 mm
User Library-TYPE-C-31-M-14.step
MICRO_603 resistor 102
micro_crystal 5x3
MICRO_led
micro_MIC5219
