Happily-Coding/SweepyWay/component_3d_models/Choc_V1_Keycap_MBK_White_1u.step

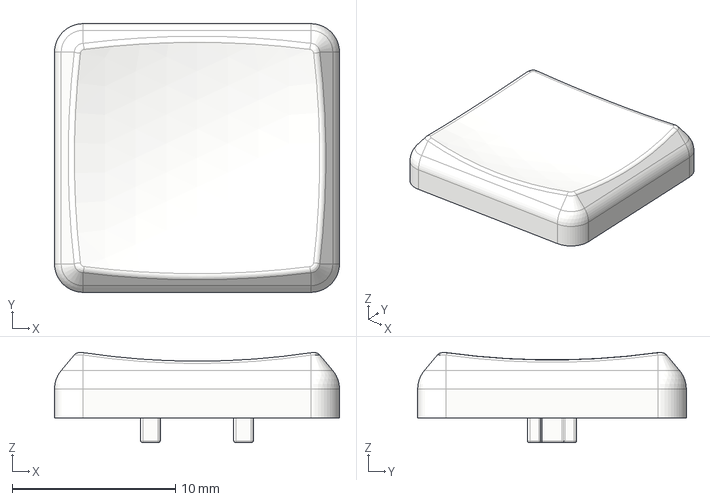
[picture p103: CAD file, 2026-01-31]
component_3d_models/Choc_V1_Keycap_MBK_White_1u.step
17.4 x 16.4 x 5.52 mm
