Happily-Coding/SweepyWay/component_3d_models/Choc_V1_Switch.step

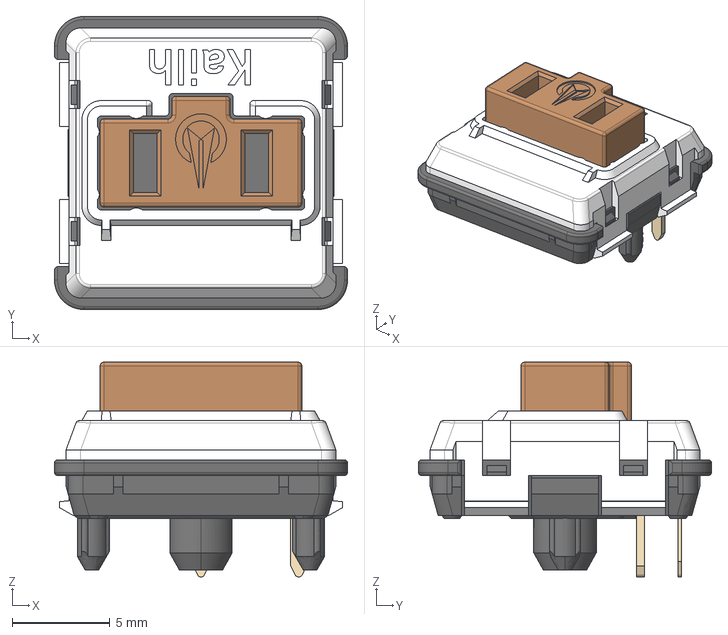
[picture p104: CAD file, 2026-01-31]
component_3d_models/Choc_V1_Switch.step
15.0 x 15.0 x 11.0 mm
