Happily-Coding/SweepyWay/component_3d_models/Choc_V1_Hotswap.step

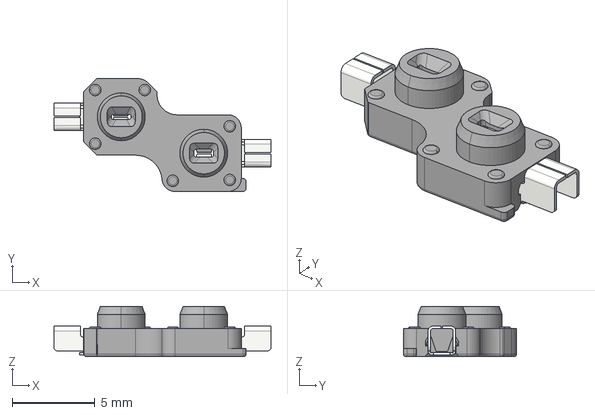
[picture p105: CAD file, 2026-01-31]
component_3d_models/Choc_V1_Hotswap.step
13.2 x 6.85 x 3.05 mm
