Happily-Coding/SweepyWay/visual_references_assembly/orden plate + switches AUR-SWP-build-left_1044x696.webp

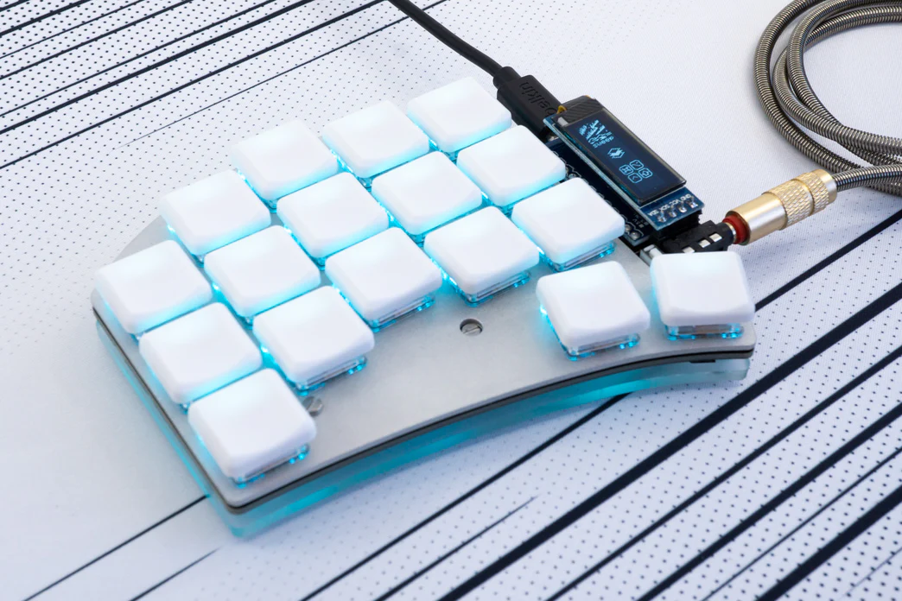
visual_references_assembly/orden plate + switches AUR-SWP-build-left_1044x696.webp
