Happily-Coding/SweepyWay/visual_references_assembly/orden plate + switches F9A5B3A4-02FF-4255-BB73-A329572225A3.webp

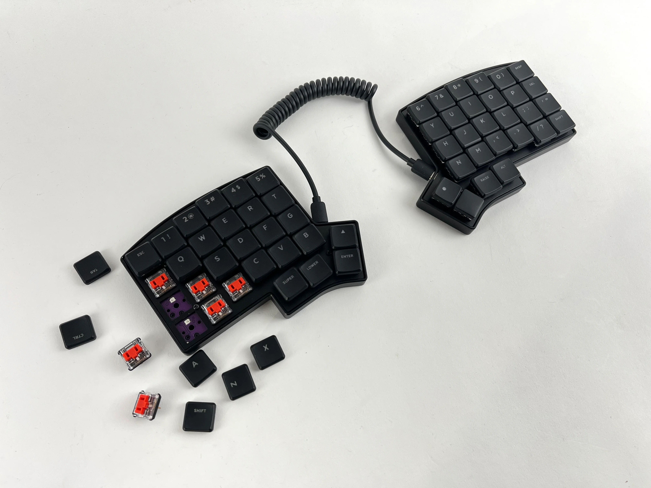
visual_references_assembly/orden plate + switches F9A5B3A4-02FF-4255-BB73-A329572225A3.webp
